Forestierr/Controle-lumieres-knx/1_Documentation/DOC_FAB/GERBER_TOP_BOT_3D.pdf

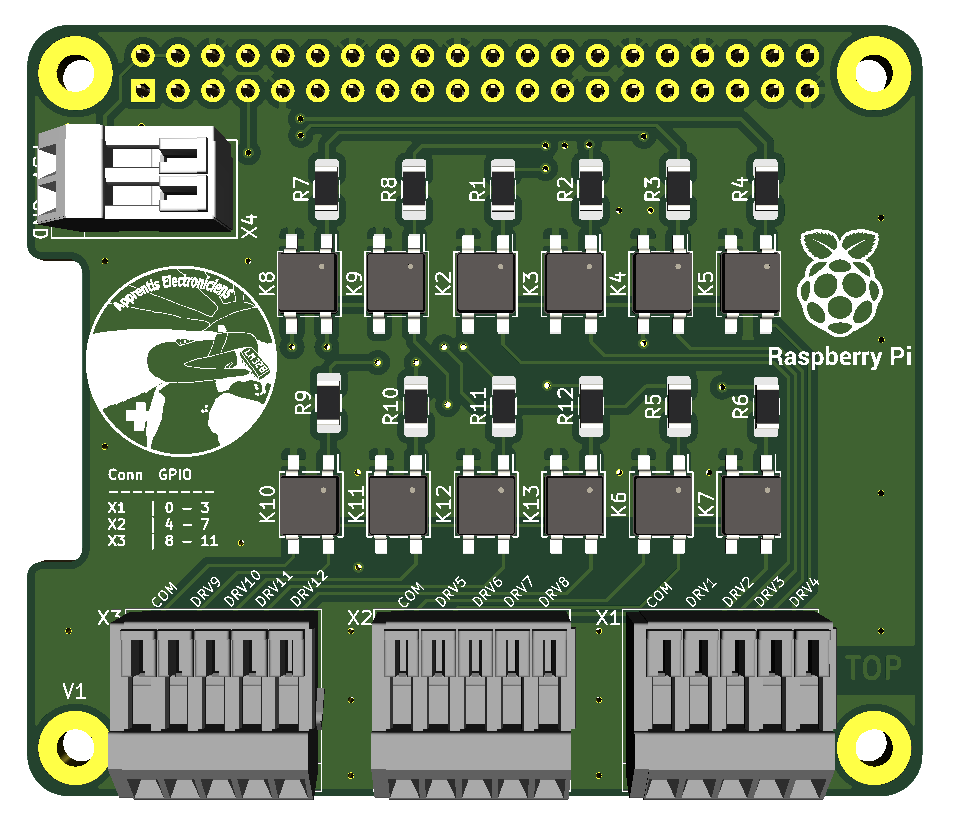
[picture p43: page 1]
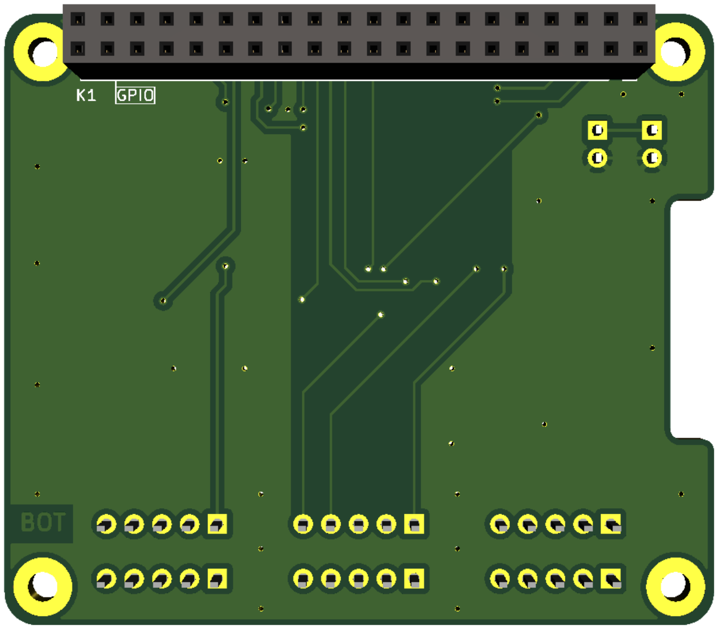
[picture p44: page 2]
