Forestierr/Controle-lumieres-knx/1_Documentation/CLASSEUR/5_Programmation/login.pdf

1 | <!DOCTYPE html>
2 | <html | | lang="fr">
3 | <head>
4 | | <meta | | charset="UTF-8">
5 | | <title>Light Control</title>
6 | | <link | | rel="icon" | | | type="image/x-icon" | | | | href="/static/img/LogoElo.ico">
7 | | <link | | rel="stylesheet" | | | href="../static/login.css/">
8 | </head>
9 | <body>
10 | | <div | | class="header">
11 | | <a | | href="#"> | | | | <img | | class="logo_img" | | src="/static/img/logo.png" | alt="logo"
| width="75%"> | | | | | </a>
12 | | <p> | {{ time }} | </p>
13 | | | <p | | class="warning"> | | | {{ warning }} | </p>
14 | | <h1>ELO Light Control</h1>
15 | | </div>
16
17 | | <form | | method="post">
18 | | <label | | for="username" | | | style="color: white">Username :</label><br>
19 | | <input | | type="text" | | | id="username" | | | | name="username"><br>
20 | | <label | | for="password" | | | style="color: white">Password :</label><br>
21 | | <input | | type="password" | | | id="password" | | | | name="password"><br>
22 | | <button | | class="btn" | | | type="submit" | | | | name="button_p1">
23 | | <img | | class="btn_img" | | | src="/static/img/img_plus.png" | | | | alt="bt+"
| width="70px">
24 | | </button>
25 | | </form>
26 | </body>
27 | </html>
28
