Forestierr/Controle-lumieres-knx/1_Documentation/CLASSEUR/5_Programmation/page1.pdf

1 <!DOCTYPE html>
2 | <html | | lang="fr">
3 <head>
4 | | <meta | | http-equiv="refresh" | | | | content="60">
5 | | <meta | | charset="UTF-8">
6 <title>Light Control</title>
7 | | <link | | rel="icon" | | | | type="image/x-icon" | | | | href="/static/img/LogoElo.ico">
8 | | <link | | rel="stylesheet" | | | | href="../static/style.css/">
9 </head>
10 <body>
11 | | <div | | class="header">
12 | | <a | | href="/settings"> | | | | | <img | | src="/static/img/logo.png" | | | alt="logo" | | width="75%">
| </a>
13 | | <p> | {{ time }} | </p>
14 | | | <p | | class="warning"> | | | | {{ warning }} | </p>
15 <h1>ELO Light Contro</h1>
16 </div>
17
18 | | <div | | class="row" | | | | id="row">
19 | | <div | | class="column-l">
20 | | <img | | src="/static/img/plan_vide.png" | | | | alt="plan" | | | | id="plan"
| style="display: none">
21 | | <canvas | | id="myCanvas" | | | | width="356px" | | | | height="451px">
22 <script>
23 | | window.onload | | = | | function() | | | {
24 | | var | | c | | = | | document.getElementById("myCanvas");
25 | | var | | ctx | | = | | c.getContext("2d");
26 | | var | | img | | = | | document.getElementById("plan");
27 | | ctx.drawImage(img, | | | | | 0, | | | 0);
28
29 | | ctx.fillStyle | | = | | "{{ color[0] }}";
30 | | ctx.fillRect(30, | | | | | 30, | | | 10, | | | 370);
31 | | ctx.fillStyle | | = | | "{{ color[1] }}";
32 | | ctx.fillRect(83, | | | | | 30, | | | 10, | | | 370);
33 | | ctx.fillStyle | | = | | "{{ color[2] }}";
34 | | ctx.fillRect(130, | | | | | 65, | | | 10, | | | 335);
35 | | ctx.fillStyle | | = | | "{{ color[3] }}";
36 | | ctx.fillRect(180, | | | | | 65, | | | 10, | | | 335);
37 | | ctx.fillStyle | | = | | "{{ color[4] }}";
38 | | ctx.fillRect(240, | | | | | 65, | | | 10, | | | 245);
39 | | ctx.fillStyle | | = | | "{{ color[5] }}";
40 | | ctx.fillRect(285, | | | | | 30, | | | 10, | | | 280);
41 | | ctx.fillStyle | | = | | "{{ color[6] }}";
42 | | ctx.fillRect(335, | | | | | 30, | | | 10, | | | 280);
43 | | ctx.fillStyle | | = | | "{{ color[7] }}";
44 | | ctx.fillRect(140, | | | | | 30, | | | 100, | | | 10);
45 }
46 </script>
47 </canvas>
48
49 <noscript>
50 | | <p | | style="color:red">JavaScript is Disable on you brother !</p>
51 | | <p | | style="color:red">To have the best use of this site, please turn
| it on.</p>
52 </noscript>
53
54 </div>
55
56 | | <form | | method="post" | | | | action="/page1" | | | | class="column-r" | | | id="grid">
57 {% for bt in button %}
58 | | <button | | class="btn" | | | | type="submit" | | | | name="button_p1" | | | value={{
| loop.index | }}>
59 | | <img | | class="btn_img" | | | | src={{ | | bt | }} | alt="bt1" | | | width="150px">
60 {% if loop.index == 8 %}
61 | | <p | | class="text_num"> | | | | P | </p>
62 {% else %}
63 | | <p | | class="text_num"> | | | | {{ loop.index }} | </p>
64 {% endif %}
65 {% if bt == "/static/img/img_off.png" %}
66 | | <p | | class="text_on"> | | | | OFF | </p>
67 {% else %}
68 | | <p | | class="text_on"> | | | | ON | </p>

69 {% endif %}
70 </button>
71 {% endfor %}
72 | | <button | class="btn" | type="submit" | name="button_p1" | | value="page_2">
73 | | <img | class="btn_img" | src="/static/img/img_plus.png" | alt="bt+"
| width="150px">
74 | | <p | class="text_num" | style="visibility: hidden"> | + | </p>
75 | | <p | class="text_on" | style="visibility: hidden"> | OFF | </p>
76 </button>
77 </form>
78 </div>
79 </body>
80 </html>
81
