Forestierr/Controle-lumieres-knx/1_Documentation/CLASSEUR/5_Programmation/page2.pdf

1 <!DOCTYPE html>
2 | <html | | lang="fr">
3 <head>
4 | | <meta | | http-equiv="refresh" | | | | content="60">
5 | | <meta | | charset="UTF-8">
6 <title>Light Control</title>
7 | | <link | | rel="icon" | | | | type="image/x-icon" | | | | href="/static/img/LogoElo.ico">
8 | | <link | | rel="stylesheet" | | | | href="../static/style.css/">
9 </head>
10 <body>
11 | | <div | | class="header">
12 | | <a | | href="/settings"> | | | | | <img | | src="/static/img/logo.png" | | | alt="logo" | | width="75%">
| </a>
13 | | <p> | {{ time }} | </p>
14 | | | <p | | class="warning"> | | | | {{ warning }} | </p>
15 <h1>ELO Light Control 2</h1>
16 </div>
17
18 | | <div | | class="row" | | | | id="row">
19 | | <div | | class="column-l">
20 | | <img | | src="/static/img/plan_vide.png" | | | | alt="plan" | | | | id="plan"
| style="display: none">
21 | | <canvas | | id="myCanvas" | | | | width="356px" | | | | height="451px"></canvas>
22 | | <p> | {{ color }}</p>
23 <script>
24 | | window.onload | | = | | function() | | | {
25 | | var | | c | | = | | document.getElementById("myCanvas");
26 | | var | | ctx | | = | | c.getContext("2d");
27 | | var | | img | | = | | document.getElementById("plan");
28 | | ctx.drawImage(img, | | | | | 0, | | | 0);
29
30 | | ctx.fillStyle | | = | | "{{ color[0] }}";
31 | | ctx.fillRect(30, | | | | | 30, | | | 10, | | | 370);
32 | | ctx.fillStyle | | = | | "{{ color[1] }}";
33 | | ctx.fillRect(83, | | | | | 30, | | | 10, | | | 370);
34 | | ctx.fillStyle | | = | | "{{ color[2] }}";
35 | | ctx.fillRect(130, | | | | | 65, | | | 10, | | | 335);
36 | | ctx.fillStyle | | = | | "{{ color[3] }}";
37 | | ctx.fillRect(180, | | | | | 65, | | | 10, | | | 335);
38 | | ctx.fillStyle | | = | | "{{ color[4] }}";
39 | | ctx.fillRect(240, | | | | | 65, | | | 10, | | | 245);
40 | | ctx.fillStyle | | = | | "{{ color[5] }}";
41 | | ctx.fillRect(285, | | | | | 30, | | | 10, | | | 280);
42 | | ctx.fillStyle | | = | | "{{ color[6] }}";
43 | | ctx.fillRect(335, | | | | | 30, | | | 10, | | | 280);
44 | | ctx.fillStyle | | = | | "{{ color[7] }}";
45 | | ctx.fillRect(140, | | | | | 30, | | | 100, | | | 10);
46 }
47 </script>
48 </div>
49
50 | | <form | | method="post" | | | | action="/page2" | | | | class="column-r" | | | id="grid">
51 {% for bt in button %}
52 | | <button | | class="btn" | | | | type="submit" | | | | name="button_p1" | | | value={{
| loop.index | }}>
53 | | <img | | class="btn_img" | | | | src={{ | | bt | }} | alt="bt1" | | | width="150px">
54 {% if loop.index == 1 %}
55 | | <p | | class="text_num"> | | | | ON | </p>
56 {% elif loop.index == 2 %}
57 | | <p | | class="text_num"> | | | | OFF | </p>
58 {% elif loop.index == 3 %}
59 | | <p | | class="text_num"> | | | | 1/2 | </p>
60 {% elif loop.index == 4 %}
61 | | <p | | class="text_num"> | | | | G | </p>
62 {% elif loop.index == 5 %}
63 | | <p | | class="text_num"> | | | | D | </p>
64 | {% elif loop.index > 5 and loop.index | < 9 %}
65 | <p class="text_num"> | N/C | </p>
66 {% else %}
67 | | <p | | class="text_num"> | | | | {{ loop.index }} | </p>
68 {% endif %}
69 {% if bt == "/static/img/img_off.png" %}

70 | | <p | class="text_on"> | OFF | </p>
71 {% else %}
72 | | <p | class="text_on"> | ON | </p>
73 {% endif %}
74 </button>
75 {% endfor %}
76 | | <button | class="btn" | type="submit" | | name="button_p1" | | value="page_1">
77 | | <img | class="btn_img" | src="/static/img/img_plus.png" | | alt="bt+"
| width="150px">
78 | | <p | class="text_num" | style="visibility: hidden"> | | + | </p>
79 | | <p | class="text_on" | style="visibility: hidden"> | | OFF | </p>
80 </button>
81 </form>
82 </div>
83 </body>
84 </html>
85
