Forestierr/Controle-lumieres-knx/1_Documentation/CLASSEUR/5_Programmation/settings.pdf

1 | <!DOCTYPE html>
2 | <html | | lang="fr">
3 | <head>
4 | | <meta | | http-equiv="refresh" | | content="60">
5 | | <meta | | charset="UTF-8">
6 | | <title>Settings</title>
7 | | <link | | rel="icon" | | type="image/x-icon" | | | | href="/static/img/LogoElo.ico">
8 | | <link | | rel="stylesheet" | | href="../static/settings.css/">
9 | </head>
10 | <body>
11 | | <div | | class="header">
12 | | <a | | href="/settings"> | | | <img | | src="/static/img/logo.png" | | alt="logo" | width="75%">
| </a>
13 | | <p> | {{ time }} | </p>
14 | | | <p | | class="warning"> | | {{ warning }} | </p>
15 | | <h1>Settings</h1>
16 | | </div>
17
18 | | <div | | class="content">
19 | | <div | | class="form_setting">
20 | | <form | | method="post" | | name="">
21 | {% for setting in settings %}
22 | | <p> | {{ setting[0] }} | </p>
23 | {% if setting[1] == 'on' %}
24 | | <input | | type="checkbox" | | name="{{ setting[0] }}" | | | | value="on"
| class="btn_check" | | | | checked>
25 | {% else %}
26 | | <input | | type="checkbox" | | name="{{ setting[0] }}" | | | | value="on"
| class="btn_check">
27 | {% endif %}
28 | | <input | | type="time" | | id="appt" | | | | name="time {{ setting[0] }}"
| value="{{ setting[2] }}" | | | | required>
29 | {% endfor %}
30 | | </br>
31 | | </br>
32 | | <button | | type="submit" | | value="Submit" | | | | class="btn_submit">Modifier et
| retour</button>
33 | | </form>
34 | | </div>
35 | | </div>
36 | </body>
37 | </html>
