Forestierr/Controle-lumieres-knx/1_Documentation/IMG_WIKI/IMG_CODE/html/html_reload.png

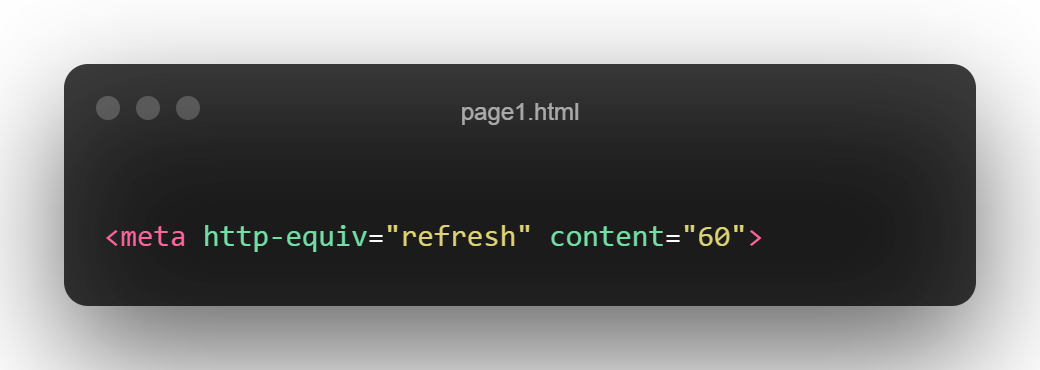
1_Documentation/IMG_WIKI/IMG_CODE/html/html_reload.png
