Forestierr/Controle-lumieres-knx/1_Documentation/IMG_WIKI/IMG_CODE/python/code_autorized_ip.png

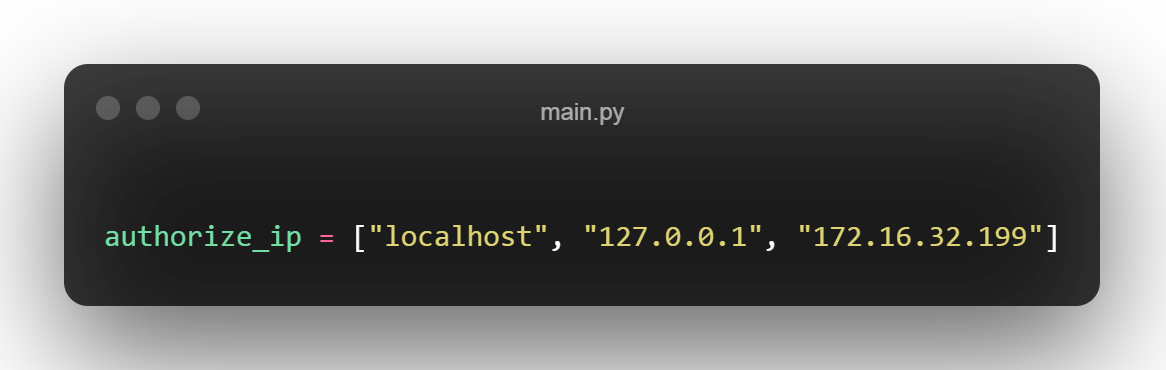
1_Documentation/IMG_WIKI/IMG_CODE/python/code_autorized_ip.png
