Forestierr/Controle-lumieres-knx/1_Documentation/IMG_WIKI/IMG_CODE/python/code_fonction_page.png

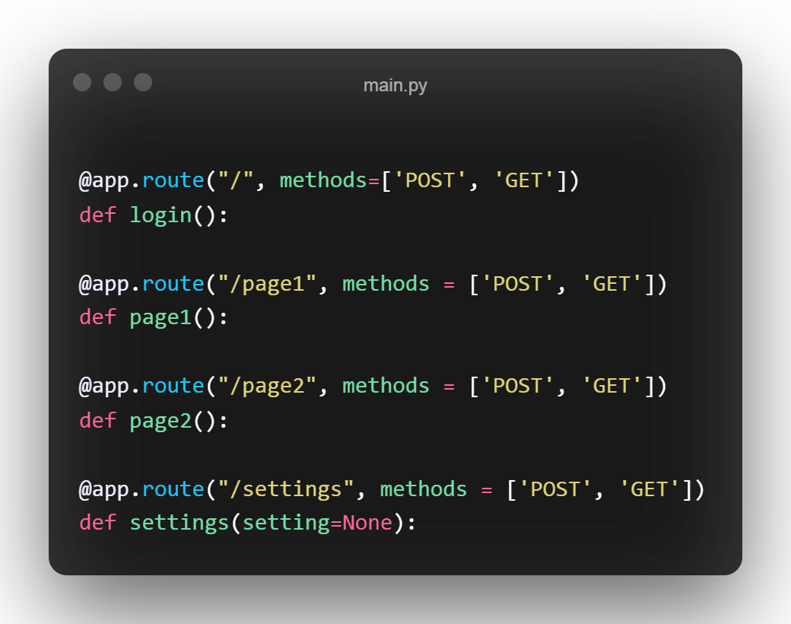
1_Documentation/IMG_WIKI/IMG_CODE/python/code_fonction_page.png
