Forestierr/Controle-lumieres-knx/1_Documentation/IMG_WIKI/IMG_CODE/python/code_user_class.png

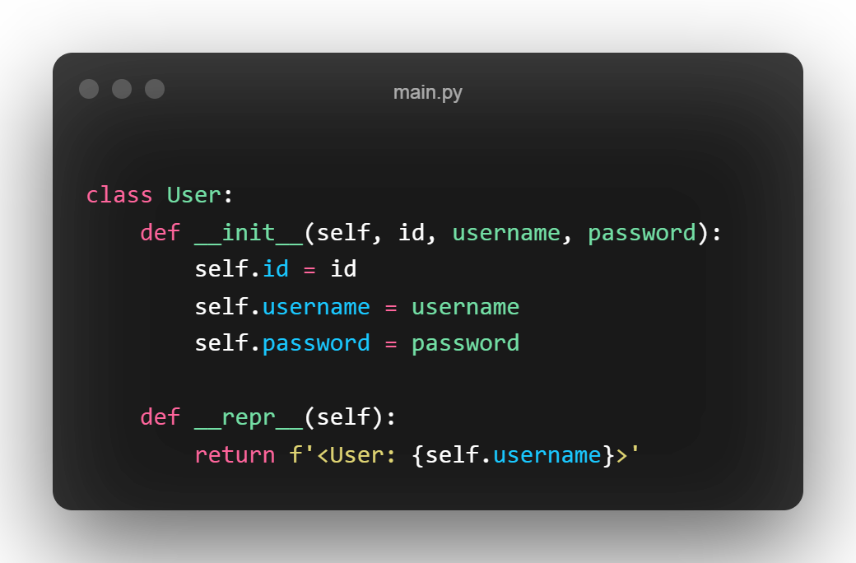
1_Documentation/IMG_WIKI/IMG_CODE/python/code_user_class.png
