Forestierr/Controle-lumieres-knx/1_Documentation/IMG_WIKI/IMG_GUI/v1/login.png

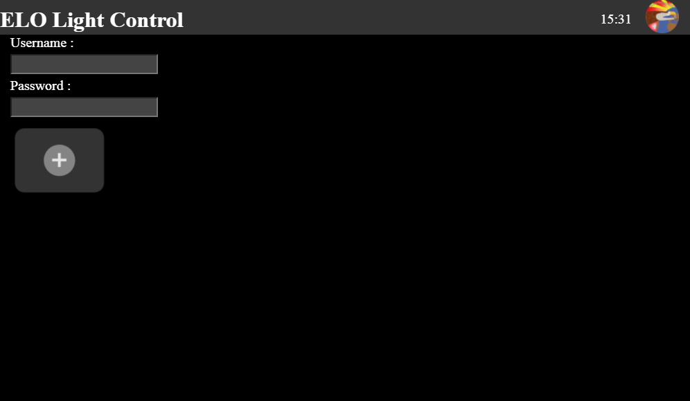
1_Documentation/IMG_WIKI/IMG_GUI/v1/login.png
