Forestierr/Controle-lumieres-knx/1_Documentation/IMG_WIKI/lightcontrol.service.png

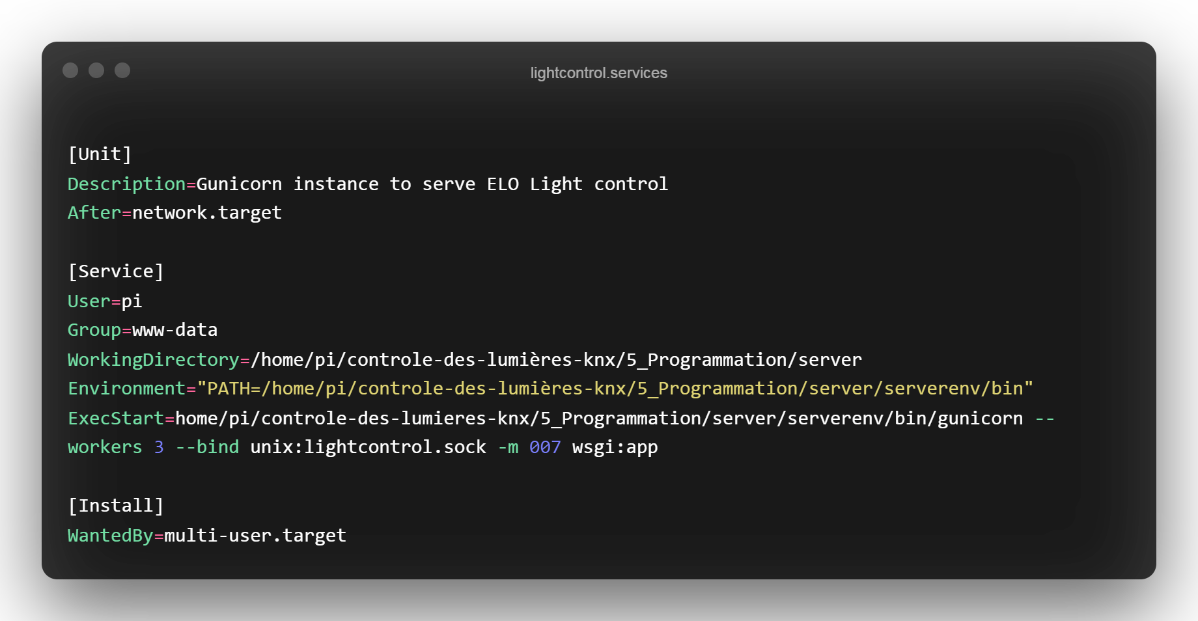
1_Documentation/IMG_WIKI/lightcontrol.service.png
