Forestierr/Controle-lumieres-knx/1_Documentation/IMG_WIKI/server.csr.png

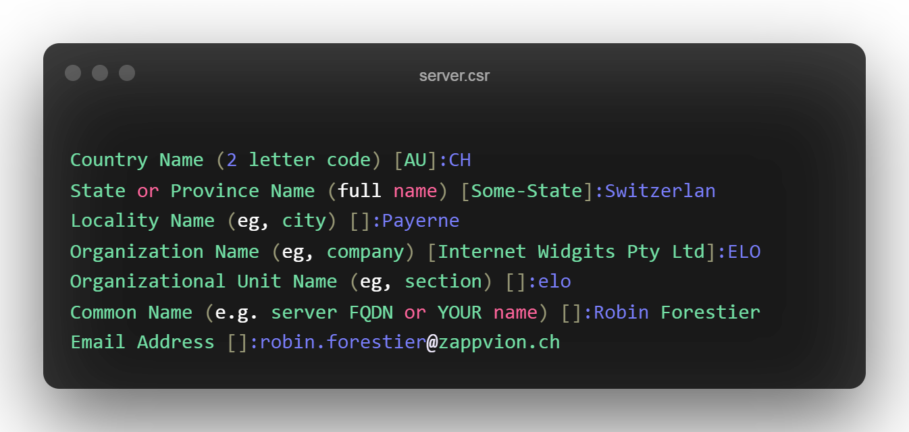
1_Documentation/IMG_WIKI/server.csr.png
