Forestierr/Controle-lumieres-knx/1_Documentation/shema_ABB_USU4.2.png

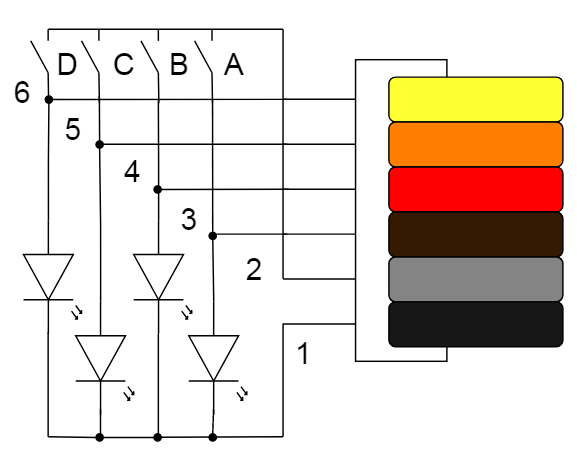
1_Documentation/shema_ABB_USU4.2.png
