Forestierr/Controle-lumieres-knx/1_Documentation/USU4.2.png

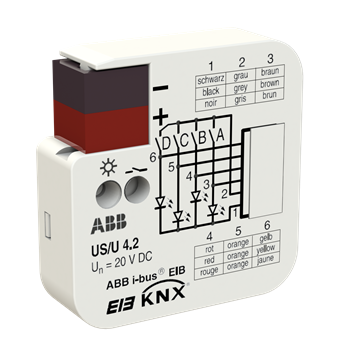
1_Documentation/USU4.2.png
