Forestierr/Controle-lumieres-knx/1_Documentation/DOC_FAB/bom/1.png

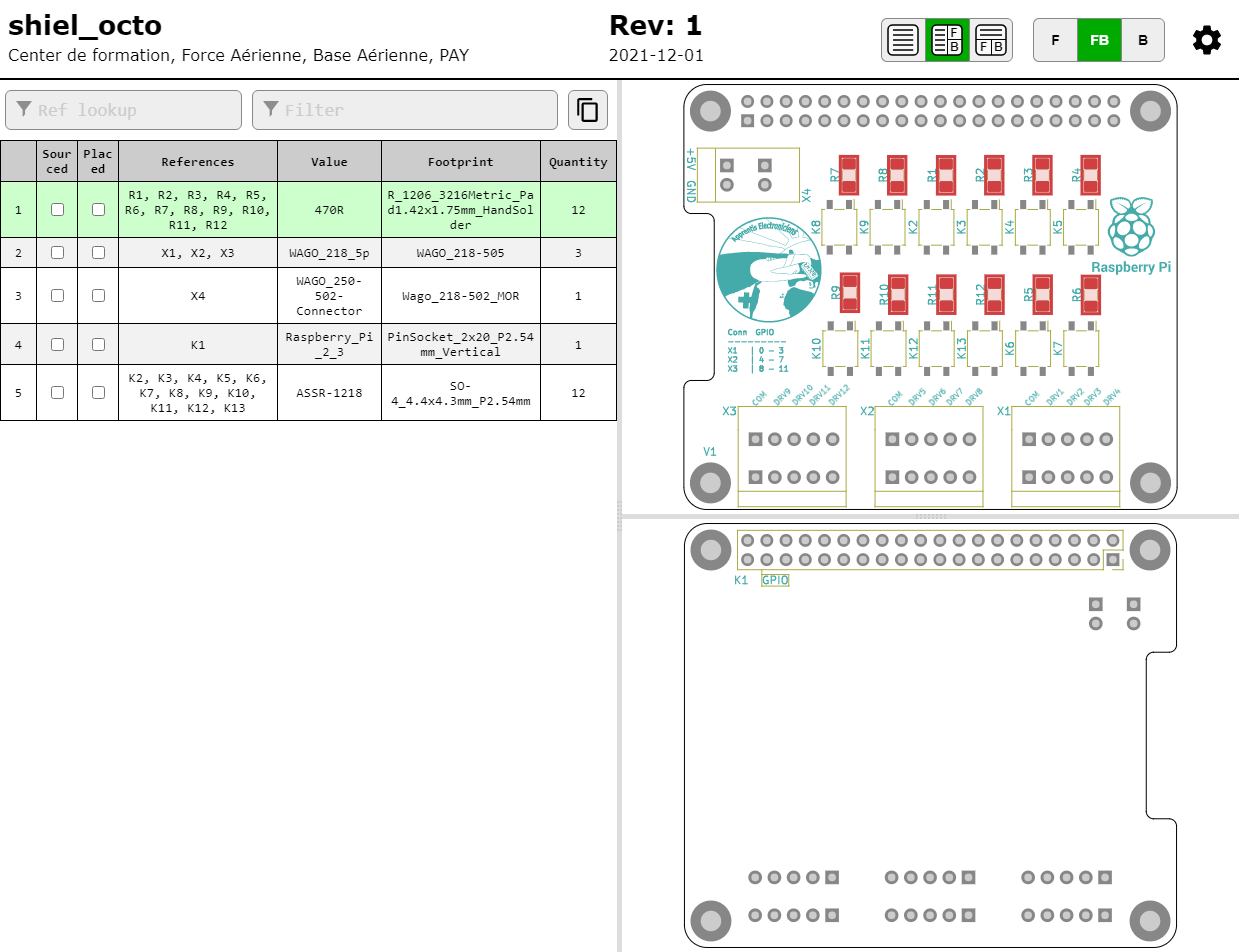
1_Documentation/DOC_FAB/bom/1.png
