Forestierr/Controle-lumieres-knx/1_Documentation/IMG_WIKI/shema_block.pdf

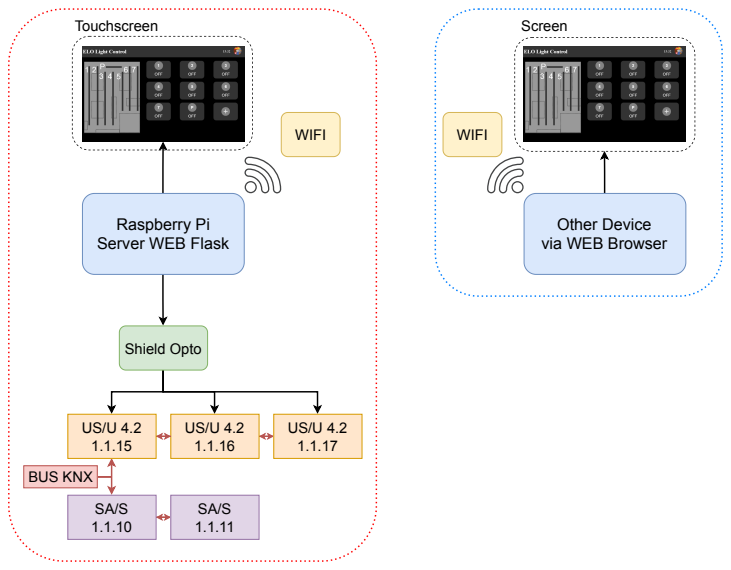
[picture p85: page 1]
WIFI; Shield Opto; BUS KNX; Touchscreen; Screen

Raspberry Pi
Server WEB Flask

Other Device
via WEB Browser
